geaz/tableDisco/pcb/tableDisco.sch

## KiCad design pcb/tableDisco.sch (2020-03-17)

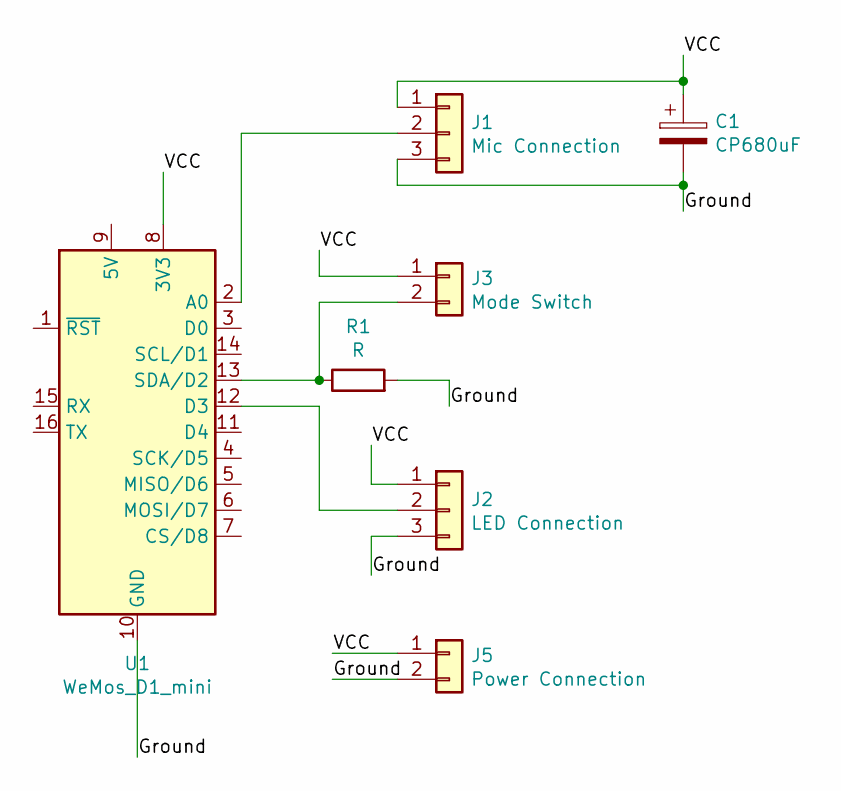
[picture p19: schematic tableDisco.sch]

Parts:
C1: CP680uF; CP_Radial_D6.3mm_P2.50mm
J1: Mic Connection; SolderWirePad_1x03_P3.81mm_Drill1.2mm
J2: LED Connection; SolderWirePad_1x03_P3.81mm_Drill1.2mm
J3: Mode Switch; SolderWirePad_1x02_P3.81mm_Drill0.8mm
J5: Power Connection; SolderWirePad_1x02_P3.81mm_Drill0.8mm
R1: R; R_Axial_DIN0207_L6.3mm_D2.5mm_P10.16mm_Horizontal
U1: WeMos_D1_mini; WEMOS_D1_mini_light

Connections:
Ground: C1.2, J1.3, J2.3, J5.2, R1.2, U1.10 (GND)
unnamed: J1.2, U1.2 (A0)
unnamed: J2.2, U1.12 (D3)
unnamed: J3.2, R1.1, U1.13 (SDA/D2)
VCC: C1.1, J1.1, J2.1, J3.1, J5.1, U1.8 (3V3)
